neuroidss/FreeEEG8-alpha/Arduino/Sender_BLE5_Data_2M_alpha_fix_esp32_s3_cmd/ADS131M08.h

#ifndef ADS131M08_h
#define ADS131M08_h

#include "Arduino.h"
#include "SPI.h"

// Uncomment this define to enable DMA-backed SPI transfers for bulk ADC data reads.
// This uses SPIClass::transferBytes, which on ESP32 typically uses DMA.
// This may improve stability and performance for high-speed data acquisition.
#define USE_DMA_FOR_ADC_READ 

typedef union {
    int32_t i;
    float f;
    uint16_t u[2];
    uint8_t b[4];
} flex32_t;


/* Adc Structure. Ch can be read as int32 or float*/
struct AdcOutput
{
  uint16_t status;
  flex32_t ch[8];
};


#define DRDY_STATE_LOGIC_HIGH 0 // DEFAULS
#define DRDY_STATE_HI_Z 1

#define POWER_MODE_VERY_LOW_POWER 0
#define POWER_MODE_LOW_POWER 1
#define POWER_MODE_HIGH_RESOLUTION 2 // DEFAULT

enum ADS131M08_PgaGain
{
  PGA_1 = 0,
  PGA_2 = 1,
  PGA_4 = 2,
  PGA_8 = 3,
  PGA_16 = 4,
  PGA_32 = 5,
  PGA_64 = 6,
  PGA_128 = 7,
  PGA_INVALID
};

#define INPUT_CHANNEL_MUX_AIN0P_AIN0N 0 // Default
#define INPUT_CHANNEL_MUX_INPUT_SHORTED 1
#define INPUT_CHANNEL_MUX_POSITIVE_DC_TEST_SIGNAL 2
#define INPUT_CHANNEL_MUX_NEGATIVE_DC_TEST_SIGNAL 3

#define OSR_128 0
#define OSR_256 1
#define OSR_512 2
#define OSR_1024 3      // defaulT
#define OSR_2048 4
#define OSR_4096 5
#define OSR_8192 6
#define OSR_16384 7

#define WAIT_TIME_128 856  
#define WAIT_TIME_256 1112
#define WAIT_TIME_512 1624
#define WAIT_TIME_1024 2648
#define WAIT_TIME_2048 4696
#define WAIT_TIME_4096 8792
#define WAIT_TIME_8192 16984
#define WAIT_TIME_16384 33368

// Commands
#define CMD_NULL 0x0000 // This command gives the STATUS REGISTER
#define CMD_RESET 0x0011
#define CMD_STANDBY 0x0022
#define CMD_WAKEUP 0x0033
#define CMD_LOCK 0x0555
#define CMD_UNLOCK 0x0655
#define CMD_READ_REG 0xA000 // 101a aaaa annn nnnn   a=adress  n=numero de registros-1
#define CMD_WRITE_REG 0x6000

// Responses
#define RSP_RESET_OK 0xFF28
#define RSP_RESET_NOK 0x0011

// Registers Read Only
#define REG_ID 0x00
#define REG_STATUS 0x01

// Registers Global Settings across channels
#define REG_MODE 0x02
#define REG_CLOCK 0x03
#define REG_GAIN1 0x04
#define REG_GAIN2 0x05
#define REG_CFG 0x06
#define THRSHLD_MSB 0x07
#define THRSHLD_LSB 0x08

// Registers Channel 0 Specific
#define REG_CH0_CFG 0x09
#define REG_CH0_OCAL_MSB 0x0A
#define REG_CH0_OCAL_LSB 0x0B
#define REG_CH0_GCAL_MSB 0x0C
#define REG_CH0_GCAL_LSB 0x0D

// Registers Channel 1 Specific
#define REG_CH1_CFG 0x0E
#define REG_CH1_OCAL_MSB 0x0F
#define REG_CH1_OCAL_LSB 0x10
#define REG_CH1_GCAL_MSB 0x11
#define REG_CH1_GCAL_LSB 0x12

// Registers Channel 2 Specific
#define REG_CH2_CFG 0x13
#define REG_CH2_OCAL_MSB 0x14
#define REG_CH2_OCAL_LSB 0x15
#define REG_CH2_GCAL_MSB 0x16
#define REG_CH2_GCAL_LSB 0x17

// Registers Channel 3 Specific
#define REG_CH3_CFG 0x18
#define REG_CH3_OCAL_MSB 0x19
#define REG_CH3_OCAL_LSB 0x1A
#define REG_CH3_GCAL_MSB 0x1B
#define REG_CH3_GCAL_LSB 0x1C

// Registers Channel 4 Specific
#define REG_CH4_CFG 0x1D
#define REG_CH4_OCAL_MSB 0x1E
#define REG_CH4_OCAL_LSB 0x1F
#define REG_CH4_GCAL_MSB 0x20
#define REG_CH4_GCAL_LSB 0x21

// Registers Channel 5 Specific
#define REG_CH5_CFG 0x22
#define REG_CH5_OCAL_MSB 0x23
#define REG_CH5_OCAL_LSB 0x24
#define REG_CH5_GCAL_MSB 0x25
#define REG_CH5_GCAL_LSB 0x26

// Registers Channel 6 Specific
#define REG_CH6_CFG 0x27
#define REG_CH6_OCAL_MSB 0x28
#define REG_CH6_OCAL_LSB 0x29
#define REG_CH6_GCAL_MSB 0x2A
#define REG_CH6_GCAL_LSB 0x2B

// Registers Channel 7 Specific
#define REG_CH7_CFG 0x2C
#define REG_CH7_OCAL_MSB 0x2D
#define REG_CH7_OCAL_LSB 0x2E
#define REG_CH7_GCAL_MSB 0x2F
#define REG_CH7_GCAL_LSB 0x30

// Registers MAP CRC
#define REG_MAP_CRC 0x3E

// ------------------------------------------------------------------------------------

// Mask READ_REG
#define REGMASK_CMD_READ_REG_ADDRESS 0x1F80
#define REGMASK_CMD_READ_REG_BYTES 0x007F

// Mask Register STATUS
#define REGMASK_STATUS_LOCK 0x8000
#define REGMASK_STATUS_RESYNC 0x4000
#define REGMASK_STATUS_REGMAP 0x2000
#define REGMASK_STATUS_CRC_ERR 0x1000
#define REGMASK_STATUS_CRC_TYPE 0x0800
#define REGMASK_STATUS_RESET 0x0400
#define REGMASK_STATUS_WLENGTH 0x0300
#define REGMASK_STATUS_DRDY7 0x0080
#define REGMASK_STATUS_DRDY6 0x0040
#define REGMASK_STATUS_DRDY5 0x0020
#define REGMASK_STATUS_DRDY4 0x0010
#define REGMASK_STATUS_DRDY3 0x0008
#define REGMASK_STATUS_DRDY2 0x0004
#define REGMASK_STATUS_DRDY1 0x0002
#define REGMASK_STATUS_DRDY0 0x0001

// Mask Register MODE
#define REGMASK_MODE_REG_CRC_EN 0x2000
#define REGMASK_MODE_RX_CRC_EN 0x1000
#define REGMASK_MODE_CRC_TYPE 0x0800
#define REGMASK_MODE_RESET 0x0400
#define REGMASK_MODE_WLENGTH 0x0300
#define REGMASK_MODE_TIMEOUT 0x0010
#define REGMASK_MODE_DRDY_SEL 0x000C
#define REGMASK_MODE_DRDY_HiZ 0x0002
#define REGMASK_MODE_DRDY_FMT 0x0001

// Mask Register CLOCK
#define REGMASK_CLOCK_CH7_EN 0x8000
#define REGMASK_CLOCK_CH6_EN 0x4000
#define REGMASK_CLOCK_CH5_EN 0x2000
#define REGMASK_CLOCK_CH4_EN 0x1000
#define REGMASK_CLOCK_CH3_EN 0x0800
#define REGMASK_CLOCK_CH2_EN 0x0400
#define REGMASK_CLOCK_CH1_EN 0x0200
#define REGMASK_CLOCK_CH0_EN 0x0100
#define REGMASK_CLOCK_OSR 0x001C
#define REGMASK_CLOCK_PWR 0x0003

// Mask Register GAIN
#define REGMASK_GAIN_PGAGAIN7 0x7000
#define REGMASK_GAIN_PGAGAIN6 0x0700
#define REGMASK_GAIN_PGAGAIN5 0x0070
#define REGMASK_GAIN_PGAGAIN4 0x0007
#define REGMASK_GAIN_PGAGAIN3 0x7000
#define REGMASK_GAIN_PGAGAIN2 0x0700
#define REGMASK_GAIN_PGAGAIN1 0x0070
#define REGMASK_GAIN_PGAGAIN0 0x0007

// Mask Register CFG
#define REGMASK_CFG_GC_DLY 0x1E00
#define REGMASK_CFG_GC_EN 0x0100
#define REGMASK_CFG_CD_ALLCH 0x0080
#define REGMASK_CFG_CD_NUM 0x0070
#define REGMASK_CFG_CD_LEN 0x000E
#define REGMASK_CFG_CD_EN 0x0001

// Mask Register THRSHLD_LSB
#define REGMASK_THRSHLD_LSB_CD_TH_LSB 0xFF00
#define REGMASK_THRSHLD_LSB_DCBLOCK 0x000F

// Mask Register CHX_CFG
#define REGMASK_CHX_CFG_PHASE 0xFFC0
#define REGMASK_CHX_CFG_DCBLKX_DIS0 0x0004
#define REGMASK_CHX_CFG_MUX 0x0003

// Mask Register CHX_OCAL_LSB
#define REGMASK_CHX_OCAL0_LSB 0xFF00

// Mask Register CHX_GCAL_LSB
#define REGMASK_CHX_GCAL0_LSB 0xFF00

//   --------------------------------------------------------------------

// Conversion modes
#define CONVERSION_MODE_CONT 0
#define CONVERSION_MODE_SINGLE 1

// Data Format
#define DATA_FORMAT_TWO_COMPLEMENT 0
#define DATA_FORMAT_BINARY 1

// Measure Mode
#define MEASURE_UNIPOLAR 1
#define MEASURE_BIPOLAR 0

// Clock Type
#define CLOCK_EXTERNAL 1
#define CLOCK_INTERNAL 0

// PGA Gain
#define PGA_GAIN_1 0
#define PGA_GAIN_2 1
#define PGA_GAIN_4 2
#define PGA_GAIN_8 3
#define PGA_GAIN_16 4
#define PGA_GAIN_32 5
#define PGA_GAIN_64 = 6,
#define PGA_GAIN_128 7

// Input Filter
#define FILTER_SINC 0
#define FILTER_FIR 2
#define FILTER_FIR_IIR 3

// Data Mode
#define DATA_MODE_24BITS 0
#define DATA_MODE_32BITS 1

// Data Rate
#define DATA_RATE_0 0
#define DATA_RATE_1 1
#define DATA_RATE_2 2
#define DATA_RATE_3 3
#define DATA_RATE_4 4
#define DATA_RATE_5 5
#define DATA_RATE_6 6
#define DATA_RATE_7 7
#define DATA_RATE_8 8
#define DATA_RATE_9 9
#define DATA_RATE_10 10
#define DATA_RATE_11 11
#define DATA_RATE_12 12
#define DATA_RATE_13 13
#define DATA_RATE_14 14
#define DATA_RATE_15 15

// Sync Mpdes
#define SYNC_CONTINUOUS 1
#define SYNC_PULSE 0

// DIO Config Mode
#define DIO_OUTPUT 1
#define DIO_INPUT 0

#define SPI_MASTER_DUMMY 0xFF
#define SPI_MASTER_DUMMY16 0xFFFF
#define SPI_MASTER_DUMMY32 0xFFFFFFFF

class ADS131M08
{
public:
  ADS131M08();

  void begin(uint8_t clk_pin, uint8_t miso_pin, uint8_t mosi_pin, uint8_t cs_pin, uint8_t drdy_pin,  uint8_t reset_pin);
  int8_t isDataReadySoft(byte channel);
  bool isDataReady(void);
  bool isResetStatus(void);
  bool isLockSPI(void);
  bool setDrdyFormat(uint8_t drdyFormat);
  bool setDrdyStateWhenUnavailable(uint8_t drdyState);
  bool setPowerMode(uint8_t powerMode);
  bool setChannelEnable(uint8_t channel, uint16_t enable);
  bool setChannelPGA(uint8_t channel, ADS131M08_PgaGain pga);
  ADS131M08_PgaGain getChannelPGA(uint8_t channel);
  void setGlobalChop(uint16_t global_chop);
  void setGlobalChopDelay(uint16_t delay);
  bool setInputChannelSelection(uint8_t channel, uint8_t input);
  bool setChannelOffsetCalibration(uint8_t channel, int32_t offset);
  bool setChannelGainCalibration(uint8_t channel, uint32_t gain);
  bool setOsr(uint16_t osr);
  void setFullScale(uint8_t channel, float scale);
  float getFullScale(uint8_t channel);
  void reset();
  uint16_t getId();
  uint16_t getModeReg();
  uint16_t getClockReg();
  uint16_t getCfgReg();
  AdcOutput readAdcRaw(void);
  AdcOutput readAdcFloat(void);
  uint8_t writeRegister(uint8_t address, uint16_t value);
  void writeRegisterMasked(uint8_t address, uint16_t value, uint16_t mask);
  uint16_t readRegister(uint8_t address);

private:
  uint8_t csPin;
  uint8_t drdyPin;
  uint8_t clkPin;
  uint8_t misoPin;
  uint8_t mosiPin;
  uint8_t resetPin;
  ADS131M08_PgaGain pgaGain[8];
  AdcOutput fullScale;
  AdcOutput resultRaw;
  AdcOutput resultFloat;
  SPIClass spi;

  uint32_t transfer24(uint32_t data); // Helper for 24-bit SPI transfer (retained for non-bulk command transfers)
  float scaleResult(uint8_t);
  AdcOutput scaleResult(void);
};
#endif
